chiba-yt834/Making_a_PWB_fits_into_the_ICB-33H_housing/KiCAD/6.0/icb33h_pwb_rev2.kicad_sch

## KiCad design KiCAD/6.0/icb33h_pwb_rev2.kicad_sch (2024-06-18)

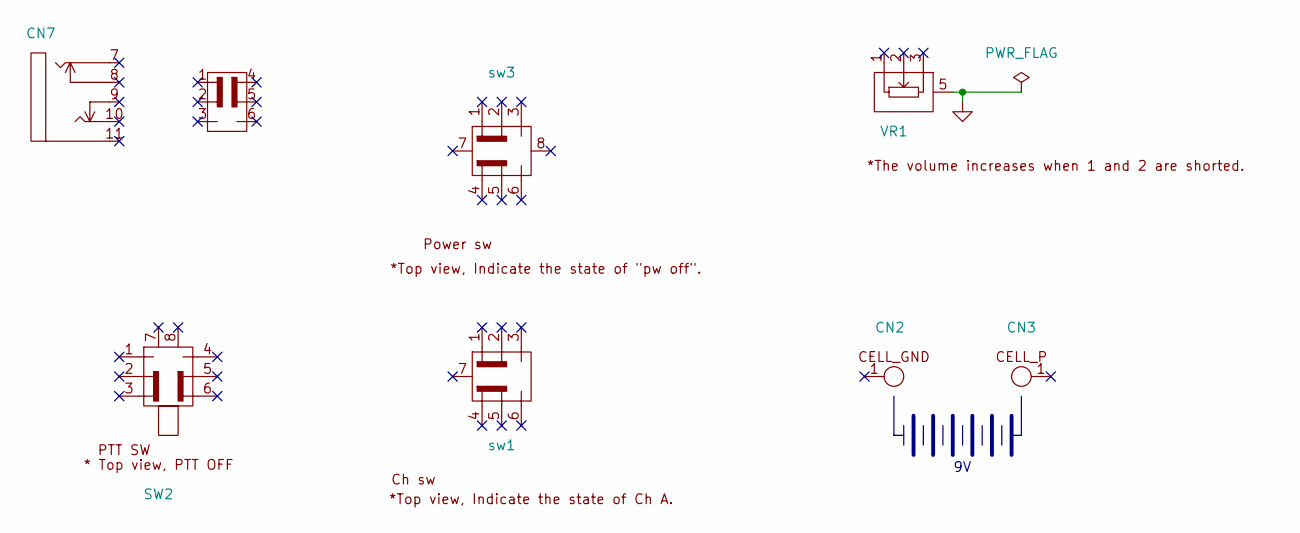
[picture p24: schematic icb33h_pwb_rev2.kicad_sch]

Parts:
CN2: icb33h_CELL_GND
CN3: icb33h_CELL_P
CN7: icb33h_ph2; icb33h_ph
SW2: icb33h_ptt_sw2; icb33h_ptt_sw_rev2
VR1: icb33h_pw_vr; icb33h_vr_rev2
sw1: icb33h_ch_sw; icb33h_sw_2
sw3: icb33h_pw_sw; icb33h_sw

Connections:
icb33h_GND: VR1.5
